TTNApeldoorn/aid-hittestress-2025/hardware/pcb/workbench/PXL_20250917_130410493.jpg

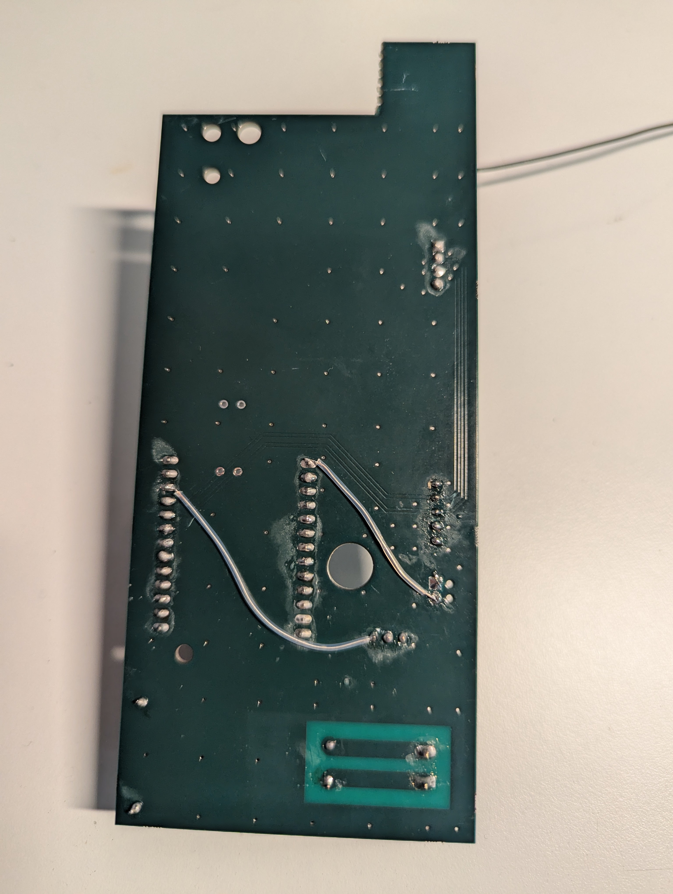
hardware/pcb/workbench/PXL_20250917_130410493.jpg
