TTNApeldoorn/aid-hittestress-2025/hardware/pcb/workbench/PXL_20250917_130453097.jpg

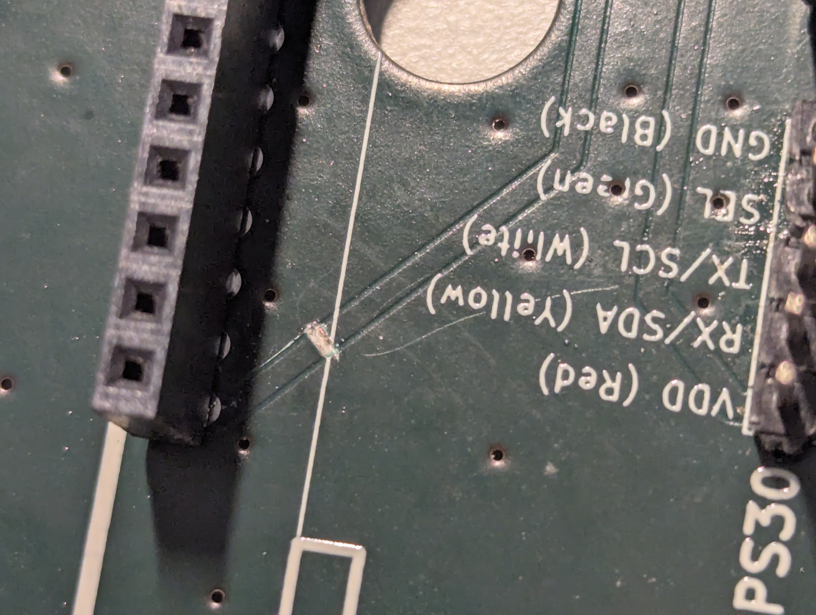
hardware/pcb/workbench/PXL_20250917_130453097.jpg
