TTNApeldoorn/aid-hittestress-2025/software/src/ttn.cpp

/*

TTN module
Wrapper to use TTN with the LMIC library

Copyright (C) 2018 by Xose Pérez <xose dot perez at gmail dot com>

This code requires the MCCI LoRaWAN LMIC library
by IBM, Matthis Kooijman, Terry Moore, ChaeHee Won, Frank Rose
https://github.com/mcci-catena/arduino-lmic

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
You should have received a copy of the GNU General Public License
along with this program.  If not, see <http://www.gnu.org/licenses/>.
*/

#include <lmic.h>
#include <hal/hal.h>
#include <SPI.h>
#include <Preferences.h>
#include "utilities.h"

// -----------------------------------------------------------------------------
// Globals
// -----------------------------------------------------------------------------


const lmic_pinmap lmic_pins = {
    .nss =  RADIO_CS_PIN,
    .rxtx = LMIC_UNUSED_PIN,
    .rst =  RADIO_RST_PIN,
    .dio = {RADIO_DIO0_PIN, RADIO_DIO1_PIN, RADIO_DIO2_PIN}
};

//static osjob_t sendjob;
static int spreadFactor = DR_SF7;
//static int joinStatus = EV_JOINING;
//static const unsigned TX_INTERVAL = 30;
//static String lora_msg = "";


// Message counter, stored in RTC memory, survives deep sleep.
static RTC_DATA_ATTR uint32_t count = 1;

// callbacks
static void (*rxCallback)(unsigned int, uint8_t*, unsigned int) = NULL;     
static void (*txCallback)(void) = NULL;

// forward decl.
static void parseHex( u1_t *byteBuffer, const char* str);
static void parseHexReverse( u1_t *byteBuffer, const char* str);
static void printKeys(u4_t netid, devaddr_t devaddr, u1_t* nwkKey, u1_t* artKey);

// handle TTN OTAA keys
static char deveui[32];  // generated from board id
extern void os_getDevEui (u1_t* buf) { parseHexReverse( buf, deveui);}
extern void os_getArtEui (u1_t* buf) { parseHexReverse( buf, APPEUI);}
extern void os_getDevKey (u1_t* buf) { parseHex( buf, APPKEY);}

//u1_t os_getRegion (void) { return LMIC_regionCode(0); } 

// -----------------------------------------------------------------------------
// Private methods
// -----------------------------------------------------------------------------

void onEvent (ev_t ev)
{
    Serial.print(os_getTime());
    Serial.print(": ");
    switch (ev) {
    case EV_TXCOMPLETE:
        Serial.println(F("EV_TXCOMPLETE (includes waiting for RX windows)"));

        if (LMIC.txrxFlags & TXRX_ACK) {
            Serial.println(F("Received ack"));
            //lora_msg =  "Received ACK.";
        }
        if( txCallback != NULL) {
          txCallback();
        }

        //lora_msg = "rssi:" + String(LMIC.rssi) + " snr: " + String(LMIC.snr);

        if (LMIC.dataLen) {
            // data received in rx slot after tx
            Serial.print(F("Data Received: "));
            // Serial.write(LMIC.frame + LMIC.dataBeg, LMIC.dataLen);
            // Serial.println();
            Serial.println(LMIC.dataLen);
            Serial.println(F(" bytes of payload"));
            if( rxCallback != NULL) {
              rxCallback( LMIC.frame[LMIC.dataBeg-1], &LMIC.frame[LMIC.dataBeg], LMIC.dataLen);
            }
        }
        // Schedule next transmission
        //os_setTimedCallback(&sendjob, os_getTime() + sec2osticks(TX_INTERVAL), do_send);
        break;
    case EV_JOINING:
        Serial.println(F("EV_JOINING: -> Joining..."));
        //lora_msg = "OTAA joining....";
        //joinStatus = EV_JOINING;

        break;
    case EV_JOIN_FAILED:
        Serial.println(F("EV_JOIN_FAILED: -> Joining failed"));
        //lora_msg = "OTAA Joining failed";
        break;
    case EV_JOINED:
        Serial.println(F("EV_JOINED"));
        //lora_msg = "Joined!";
        //joinStatus = EV_JOINED;

        delay(3);
        // Disable link check validation (automatically enabled
        // during join, but not supported by TTN at this time).
        LMIC_setLinkCheckMode(0);
        // save network keys to permanent storage 
        {
          //printKeys(LMIC.netid, LMIC.devaddr, LMIC.nwkKey, LMIC.artKey);
          Preferences p;
          if( p.begin("lora", false)) {
              p.putUInt("netId", LMIC.netid);
              p.putUInt("devAddr", LMIC.devaddr);
              p.putBytes("nwkKey", LMIC.nwkKey, 16);
              p.putBytes("artKey", LMIC.artKey, 16);
              p.end();
          }
        }
        break;
    case EV_RXCOMPLETE:
        // data received in ping slot
        Serial.println(F("EV_RXCOMPLETE"));
        break;
    case EV_LINK_DEAD:
        Serial.println(F("EV_LINK_DEAD"));
        break;
    case EV_LINK_ALIVE:
        Serial.println(F("EV_LINK_ALIVE"));
        break;
    default:
        Serial.println(F("Unknown event"));
        break;
    }
}
/*
u1_t readReg (u1_t addr)
{
    hal_pin_nss(0);
    hal_spi(addr & 0x7F);
    u1_t val = hal_spi(0x00);
    hal_pin_nss(1);
    return val;
} */

bool ttn_setup(void) {
  // get unique deveui from chip id
  uint64_t chipid = ESP.getEfuseMac();   //The chip ID is essentially its MAC address(length: 6 bytes).
  sprintf(deveui, "%08X%08X", (uint16_t)(chipid >> 32), (uint32_t)chipid);
  printf("DEVEUI=%s\n", deveui);

  // LoRa SPI interface
  SPI.begin(RADIO_SCLK_PIN, RADIO_MISO_PIN, RADIO_MOSI_PIN);

#ifdef  RADIO_TCXO_ENABLE
    pinMode(RADIO_TCXO_ENABLE, OUTPUT);
    digitalWrite(RADIO_TCXO_ENABLE, HIGH);
#endif

    // LMIC init
    os_init();

    // Reset the MAC state. Session and pending data transfers will be discarded.
    LMIC_reset();

    LMIC_setClockError(MAX_CLOCK_ERROR * 1 / 100);
    // Set up the channels used by the Things Network, which corresponds
    // to the defaults of most gateways. Without this, only three base
    // channels from the LoRaWAN specification are used, which certainly
    // works, so it is good for debugging, but can overload those
    // frequencies, so be sure to configure the full frequency range of
    // your network here (unless your network autoconfigures them).
    // Setting up channels should happen after LMIC_setSession, as that
    // configures the minimal channel set.

    LMIC_setupChannel(0, 868100000, DR_RANGE_MAP(DR_SF12, DR_SF7),  BAND_CENTI);      // g-band
    LMIC_setupChannel(1, 868300000, DR_RANGE_MAP(DR_SF12, DR_SF7B), BAND_CENTI);      // g-band
    LMIC_setupChannel(2, 868500000, DR_RANGE_MAP(DR_SF12, DR_SF7),  BAND_CENTI);      // g-band
    LMIC_setupChannel(3, 867100000, DR_RANGE_MAP(DR_SF12, DR_SF7),  BAND_CENTI);      // g-band
    LMIC_setupChannel(4, 867300000, DR_RANGE_MAP(DR_SF12, DR_SF7),  BAND_CENTI);      // g-band
    LMIC_setupChannel(5, 867500000, DR_RANGE_MAP(DR_SF12, DR_SF7),  BAND_CENTI);      // g-band
    LMIC_setupChannel(6, 867700000, DR_RANGE_MAP(DR_SF12, DR_SF7),  BAND_CENTI);      // g-band
    LMIC_setupChannel(7, 867900000, DR_RANGE_MAP(DR_SF12, DR_SF7),  BAND_CENTI);      // g-band
    LMIC_setupChannel(8, 868800000, DR_RANGE_MAP(DR_FSK,  DR_FSK),  BAND_MILLI);      // g2-band
    // TTN defines an additional channel at 869.525Mhz using SF9 for class B
    // devices' ping slots. LMIC does not have an easy way to define set this
    // frequency and support for class B is spotty and untested, so this
    // frequency is not configured here.

    // Disable link check validation
    LMIC_setLinkCheckMode(0);

    // TTN uses SF9 for its RX2 window.
    LMIC.dn2Dr = DR_SF9;

    // Set data rate and transmit power for uplink (note: txpow seems to be ignored by the library)
    LMIC_setDrTxpow(spreadFactor, 14);


    Preferences p;
    p.begin("lora", true);  // we intentionally ignore failure here
    uint32_t netId = p.getUInt("netId", UINT32_MAX);
    uint32_t devAddr = p.getUInt("devAddr", UINT32_MAX);
    uint8_t nwkKey[16], artKey[16];
    bool keysgood = p.getBytes("nwkKey", nwkKey, sizeof(nwkKey)) == sizeof(nwkKey) && 
                   p.getBytes("artKey", artKey, sizeof(artKey)) == sizeof(artKey);
    p.end();  // close our prefs
    //printKeys(netId, devAddr, nwkKey, artKey);

    if (!keysgood) {
     // We have not yet joined a network, start a full join attempt
      // Make LMiC initialize the default channels, choose a channel, and
     // schedule the OTAA join
      count = 1;
      Serial.println("No session saved, joining from scratch");
      LMIC_startJoining();
    }
    else {
      Serial.println("Rejoining saved session");
      LMIC_setSession(netId, devAddr, nwkKey, artKey);
    }
    p.end();
    //do_send(&sendjob);     // Will fire up also the join
    return true;
}


// -----------------------------------------------------------------------------
// Public methods
// -----------------------------------------------------------------------------

extern void ttn_register_rxReady( void (*rxReady)(unsigned int, uint8_t*, unsigned int)) {
    rxCallback = rxReady;
}

extern void ttn_register_txReady( void (*txReady)()) {
    txCallback = txReady;
}

/// Blow away our prefs (i.e. to rejoin from scratch)
extern void ttn_erase_prefs() {
  Preferences p;
  if (p.begin("lora", false)) {
    p.clear();
    p.end();
  }
}

extern bool ttn_send(uint8_t* data, uint8_t data_size, uint8_t port) {
  // Check if there is not a current TX/RX job running
  if (LMIC.opmode & OP_TXRXPEND) {
    return false;
  }
  // Prepare upstream data transmission at the next possible time.
  // Parameters are port, data, length, confirmed
  //printf("LMIC_setTxData2 count=%d\n", count);
  LMIC.seqnoUp = count;
  //LMIC_setSeqnoUp(count);  // TODO  MM
  LMIC_setTxData2(port, data, data_size, 0);
  count++;
  return true;
}

extern bool ttn_connected() {
  return (LMIC.devaddr != 0);
}

void ttn_shutdown() {
  LMIC_shutdown();
}

void ttn_loop(void) {
    os_runloop_once();
}

// local helper fumctions
static void printKeys(u4_t netid, devaddr_t devaddr, u1_t* nwkKey, u1_t* artKey) {
  printf("netid=%d\n", netid);
  printf("devaddr=%04X\n", devaddr);

  printf("NwkSKey: %02X", nwkKey[0]);
  for (size_t i = 1; i < 16; ++i)
    printf("-%02X", nwkKey[i]);
  printf("\n");

  printf("ArtKey: %02X", artKey[0]);
  for (size_t i = 1; i < 16; ++i)
    printf("-%02X", artKey[i]);
  printf("\n");
}

// convert TTN key string big endian byte array
static void parseHex( u1_t *byteBuffer, const char* str){
  int len = strlen(str);
  for (int i = 0; i < len; i+=2){
    char substr[3];
    strncpy(substr, &(str[i]), 2);
    byteBuffer[i/2] = (u1_t)(strtol(substr, NULL, 16));
  }
}

// convert TTN key string to little endian byte array
static void parseHexReverse( u1_t *byteBuffer, const char* str){
  int len = strlen(str);
  for (int i = 0; i < len; i+=2){
    char substr[3];
    strncpy(substr, &(str[i]), 2);
    byteBuffer[((len-1)-i)/2] = (u1_t)(strtol(substr, NULL, 16));   // reverse the TTN KEY string !!
  }
}
