TTNApeldoorn/aid-hittestress-2025/software/src/gps.h

/*******************************************************************************
* file GPS.h
* TinyGPS wrapper, interface
* author Marcel Meek
*********************************************************************************/

#ifndef __GPS_H_
#define __GPS_H_

class Gps {
  public:
    Gps() {}
    bool init();
    bool read();

    float lat, lng;
    int16_t alt, hdop;
};

#endif // __GPS_H_
