TTNApeldoorn/aid-hittestress-2025/software/src/mysps30.cpp

/*
  SPS30 module

  Copyright (C) 2018 by Xose Pérez <xose dot perez at gmail dot com>

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
  You should have received a copy of the GNU General Public License
  along with this program.  If not, see <http://www.gnu.org/licenses/>.
*/

#include <sps30.h>
#include "utilities.h"
#include "mysps30.h"


// SPS30 support
//#define auto_clean_days 4,   no sense, (ESP is restarted each cycle), replaced by manual auto clean 
struct sps30_measurement m;


bool Sps30::init() {
  sensirion_i2c_init();
  int retry = 5;
  while (sps30_probe() != 0) {   
    Serial.print("SPS sensor probing failed\r\n");
    delay(500);
    if( retry-- < 0)
      return false;
  }
  return true;
}

void Sps30::startManaualFanCleaning() { 
    sps30_start_measurement();
    int ret = sps30_start_manual_fan_cleaning();
    delay(12000); // fan cleaning takes about 10 sec. so wait...
    printf("startManaualFanCleaning result: %d\n", ret);
}    

bool Sps30::read() {
  //printf("Sps30::read\n");
  pm10 = pm2_5 = pm1_0 = 0.0;

  sps30_start_measurement();  // Start of loop start fan to flow air past laser sensor
  delay(9000);                //Wait 9+1 seconds while fan is active before read data
  
  for(int i=0; i<10; i++) {
    delay( 1000);
    if( !_read()) {
      sps30_stop_measurement();
      return false;
    }    
    //printf("PM1.0=%.2f PM2.5=%.2f PM10=%.2f\n", m.mc_1p0, m.mc_2p5, m.mc_10p0);
    pm10  += m.mc_10p0;
    pm2_5 += m.mc_2p5;
    pm1_0 += m.mc_1p0;
  } 

  pm10  /= 10.0;
  pm2_5 /= 10.0; 
  pm1_0 /= 10.0;;
  //printf("PM1.0=%.2f PM2.5=%.2f PM10=%.2f\n", pm1_0, pm2_5, pm10);
  sps30_stop_measurement();  //Disables Fan 
  return true;
}


// private read
bool Sps30::_read() {
  int16_t ret;
  uint16_t data_ready;
  int16_t retry = 10;

  ret = sps30_read_data_ready(&data_ready);       // check ready
  while( ret >=0 && retry > 0 && !data_ready) {   // if ok, wait until ready
    delay( 100);
    ret = sps30_read_data_ready(&data_ready);
    retry--;
  }
  
  if( retry <= 0) {
    printf("error too many read retries\n");
    return false; // to many retries
  }
  ret = sps30_read_measurement(&m);    // read
  if( ret < 0) {
    printf("error reading measurement: %d\n", ret);
    return false;
  }
  return true;
}
